gerbilbyte/DeMoN2/Kicad/DeMoN_2.0_PLCC/DeMoN_2.0_PLCC.kicad_sch

## KiCad design Kicad/DeMoN_2.0_PLCC/DeMoN_2.0_PLCC.kicad_sch (2025-10-27)

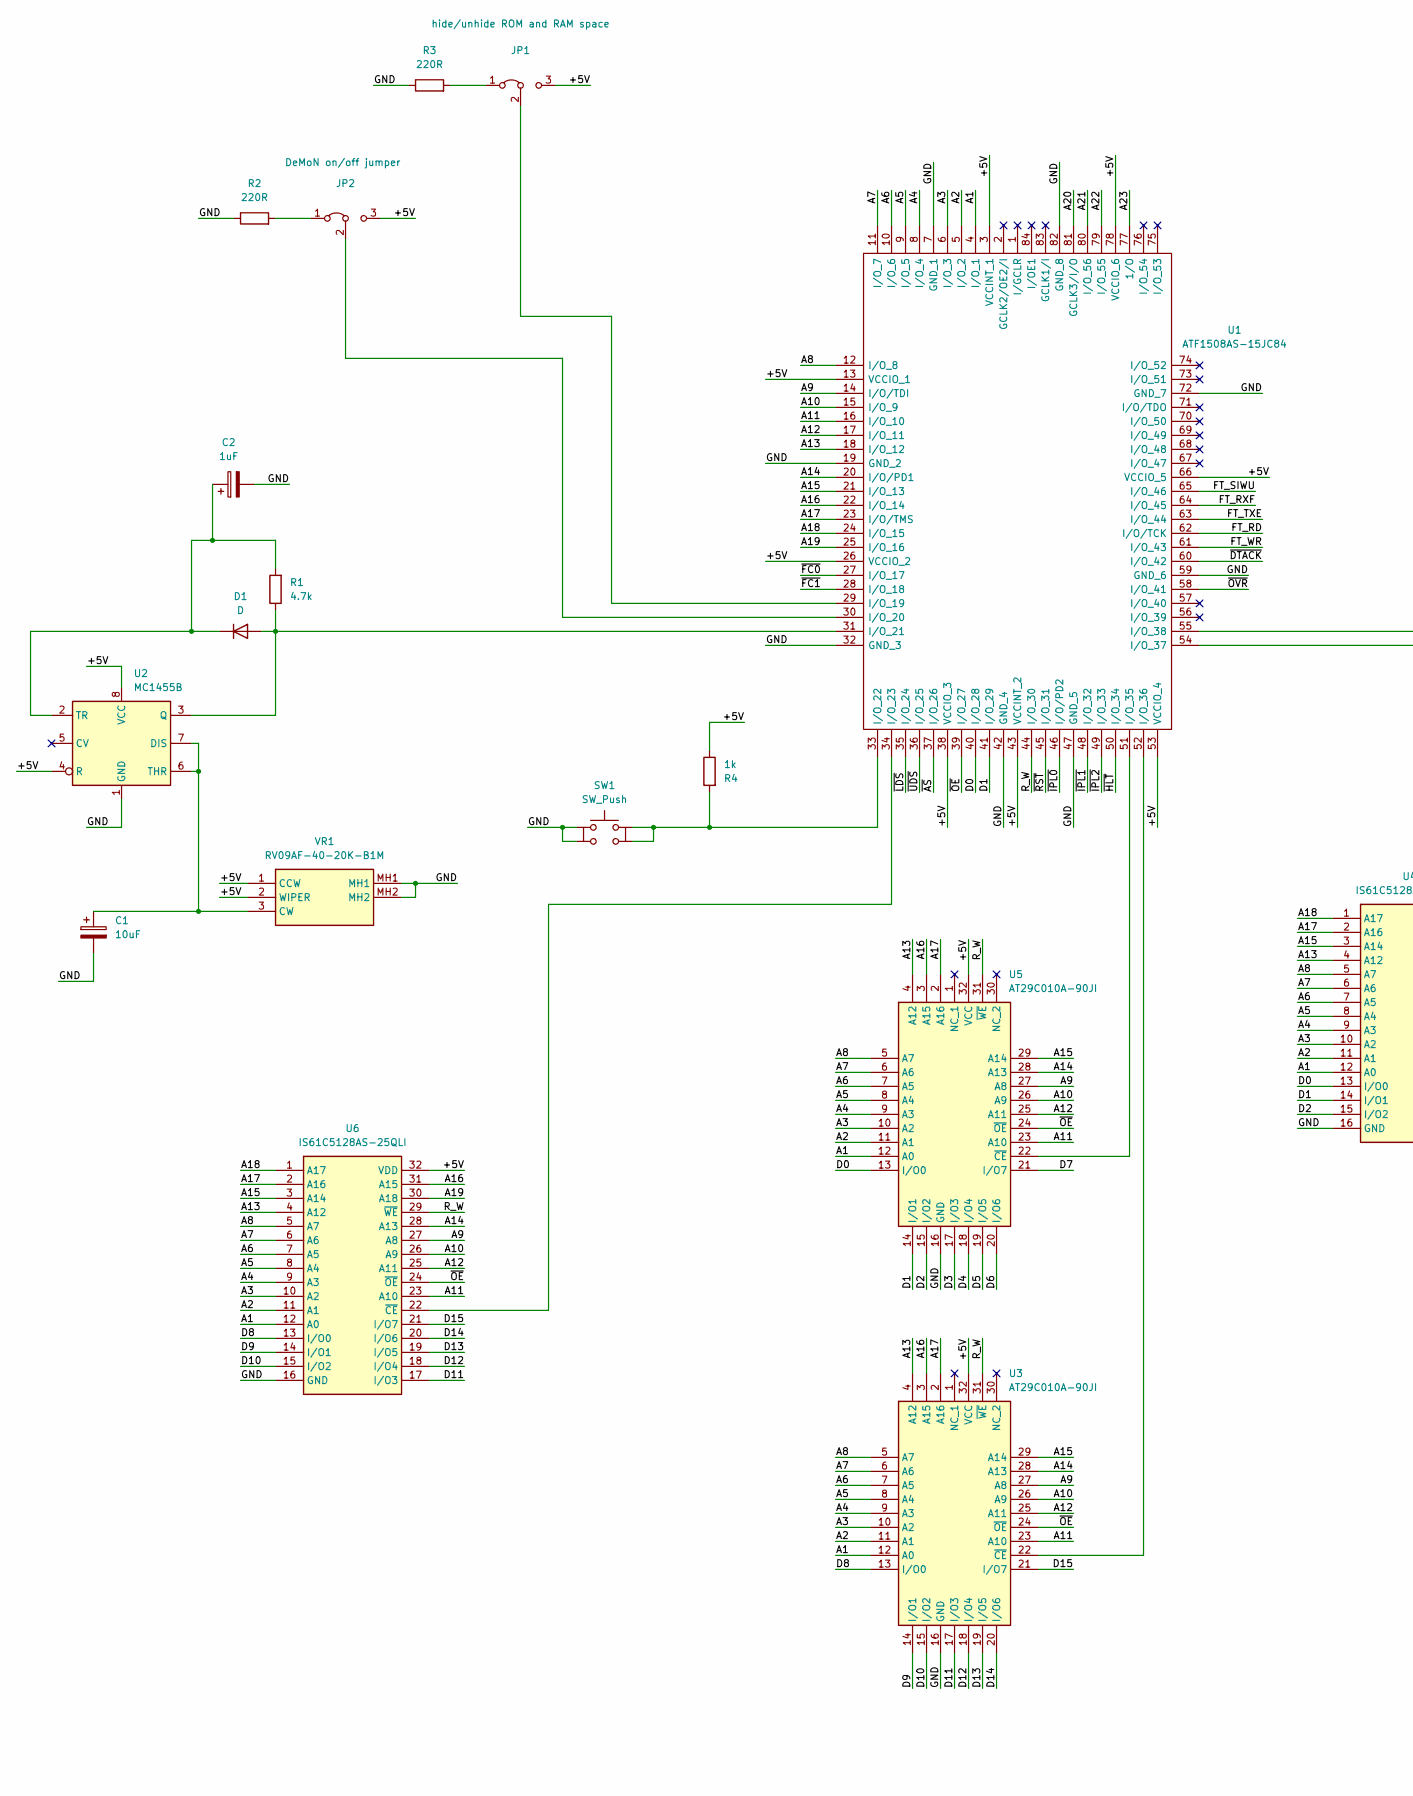
[picture p14: schematic DeMoN_2.0_PLCC.kicad_sch, part in row 1, column 1]

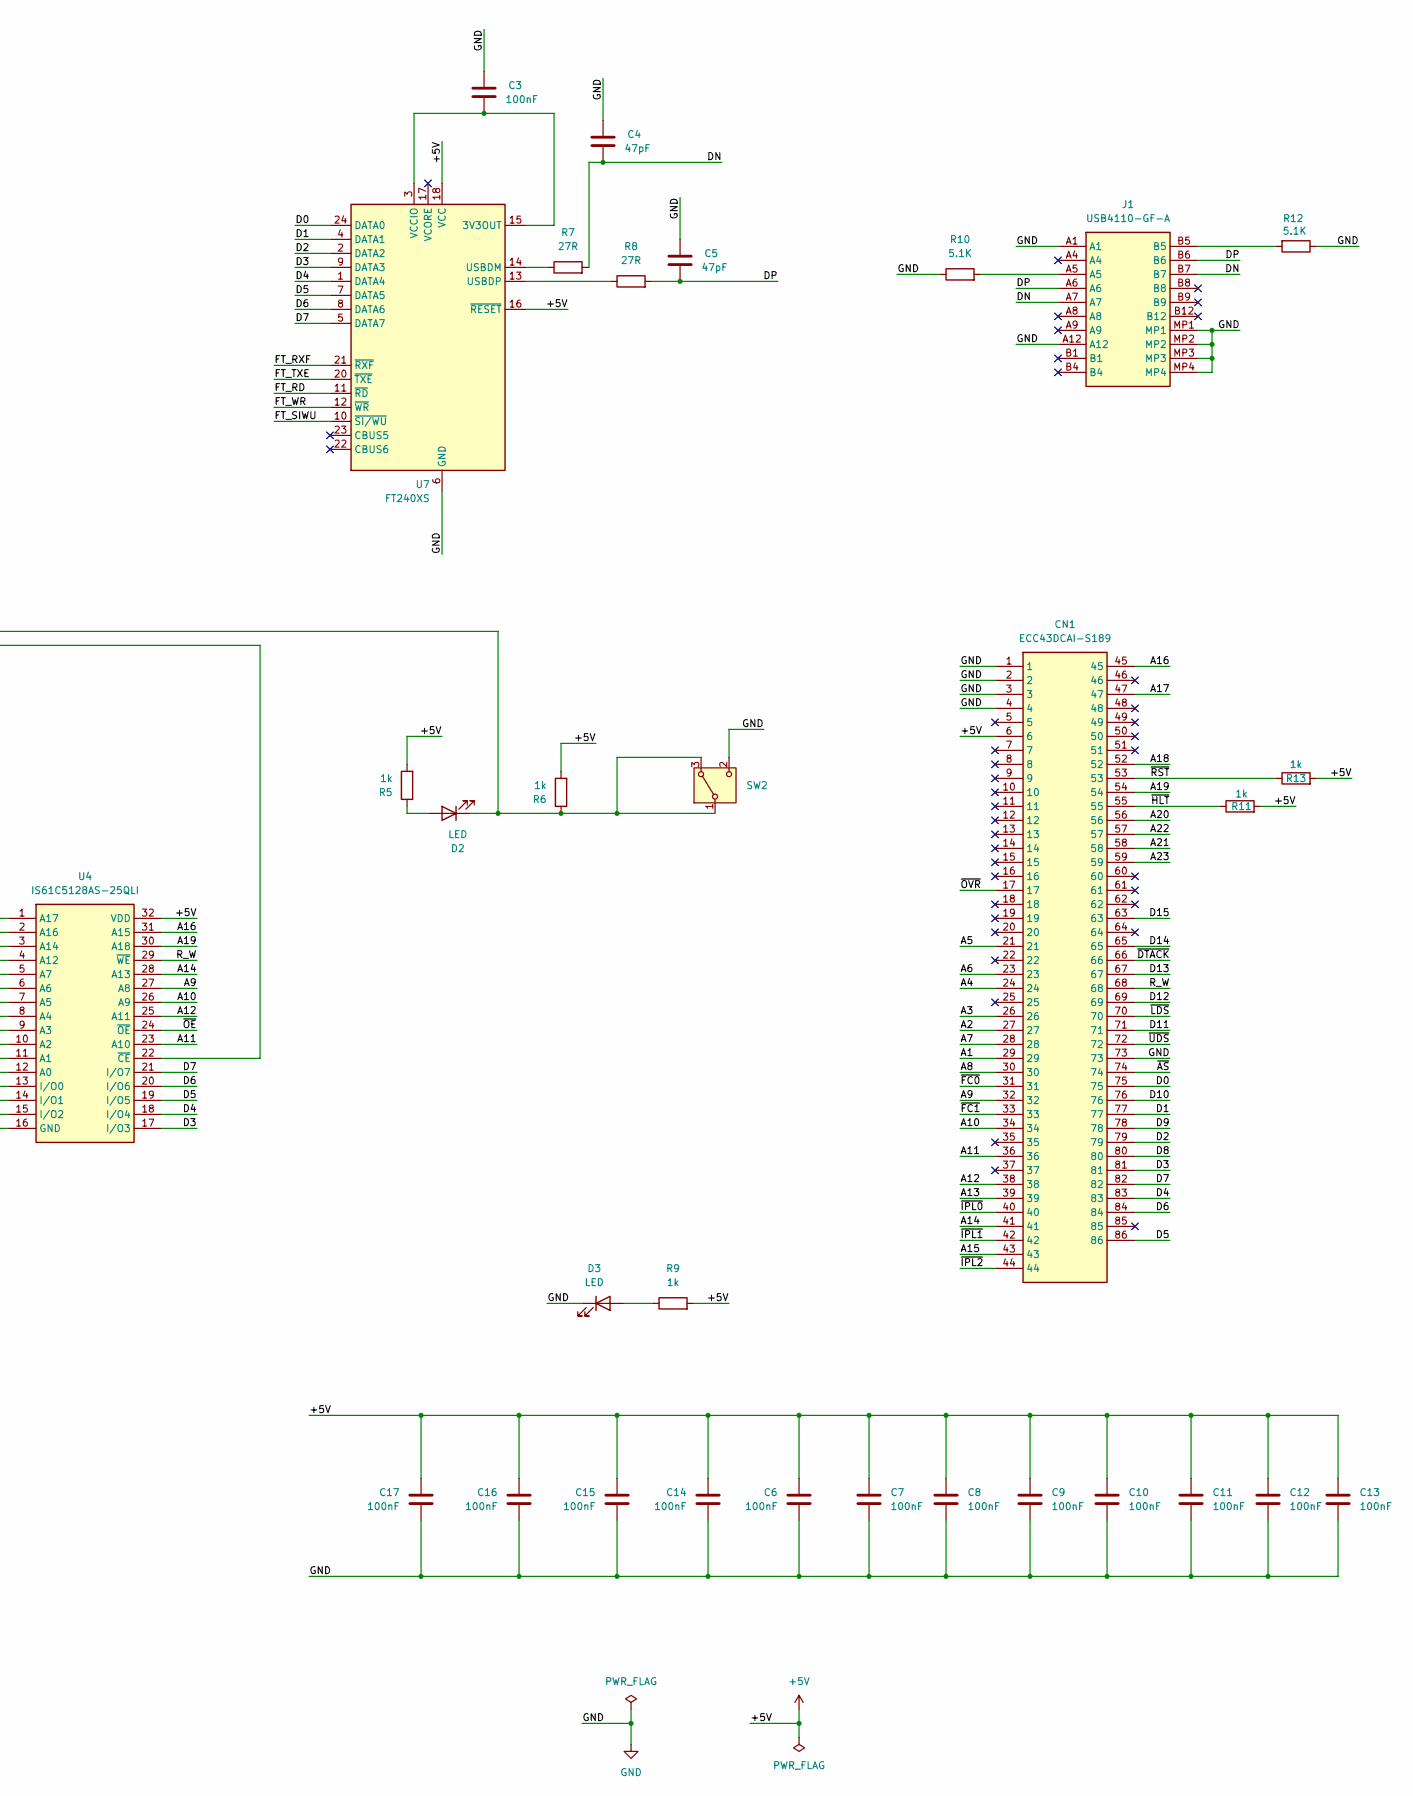
[picture p15: schematic DeMoN_2.0_PLCC.kicad_sch, part in row 1, column 2]

Parts:
C1: 10uF; CP_Radial_D5.0mm_P2.50mm
C2: 1uF; CP_Radial_D5.0mm_P2.50mm
C3, C6, C7, C8, C9, C10, C11, C12, C13, C14, C15, C16, C17: 100nF; C_1206_3216Metric_Pad1.33x1.80mm_HandSolder
C4, C5: 47pF; C_1206_3216Metric_Pad1.33x1.80mm_HandSolder
CN1: ECC43DCAI-S189; ECC43DCAIS189; Manufacturer_Part_Number ECC43DCAI-S189
D1: D; D_1206_3216Metric_Pad1.42x1.75mm_HandSolder
D2, D3: LED; LED_D3.0mm
J1: USB4110-GF-A; USB4110GFA; Mouser Part Number 640-USB4110-GF-A
JP1: hide/unhide ROM and RAM space; PinSocket_1x03_P2.54mm_Vertical
JP2: DeMoN on/off jumper; PinSocket_1x03_P2.54mm_Vertical
R1: 4.7k; R_1206_3216Metric_Pad1.30x1.75mm_HandSolder
R2, R3: 220R; R_1206_3216Metric_Pad1.30x1.75mm_HandSolder
R4, R5, R6, R9, R11, R13: 1k; R_1206_3216Metric_Pad1.30x1.75mm_HandSolder
R7, R8: 27R; R_1206_3216Metric_Pad1.30x1.75mm_HandSolder
R10, R12: 5.1K; R_1206_3216Metric_Pad1.30x1.75mm_HandSolder
SW1: SW_Push; SW_Push_2P1T_Toggle_CK_PVA1xxH1xxxxxxV2
SW2: SW_Wuerth_450301014042; SW_Slide-03_Wuerth-WS-SLTV_10x2.5x6.4_P2.54mm
U1: ATF1508AS-15JC84; PLCC-84_SMD-Socket; Manufacturer_Part_Number ATF1504AS-20JC84
U2: MC1455B; SOIC-8_3.9x4.9mm_P1.27mm
U3, U5: AT29C010A-90JI; PLCC-32_11.4x14.0mm_P1.27mm; Mouser Part Number 556-AT29C010A-90JI
U4, U6: IS61C5128AS-25QLI; SOIC127P1412X305-32N; Mouser Part Number 870-61C5128AS-25QLI
U7: FT240XS; SSOP-24_3.9x8.7mm_P0.635mm
VR1: RV09AF-40-20K-B1M; RV09AF4020KB1M; Mouser Part Number 317-2090F-1M

Connections:
+5V: C6.2, C7.1, C8.1, C9.1, C10.1, C11.1, C12.1, C13.2, C14.2, C15.2, C16.2, C17.2, CN1.6, JP1.3 (B), JP2.3 (B), R4.1, R5.2, R6.2, R9.2, R11.2, R13.2, U1.3 (VCCINT_1), U1.13 (VCCIO_1), U1.26 (VCCIO_2), U1.38 (VCCIO_3), U1.43 (VCCINT_2), U1.53 (VCCIO_4), U1.66 (VCCIO_5), U1.78 (VCCIO_6), U2.4 (R), U2.8 (VCC), U3.32 (VCC), U4.32 (VDD), U5.32 (VCC), U6.32 (VDD), U7.16 (~RESET), U7.18 (VCC), VR1.1 (CCW), VR1.2 (WIPER)
A1: CN1.29, U1.4 (I/O_1), U3.12 (A0), U4.12 (A0), U5.12 (A0), U6.12 (A0)
A2: CN1.27, U1.5 (I/O_2), U3.11 (A1), U4.11 (A1), U5.11 (A1), U6.11 (A1)
A3: CN1.26, U1.6 (I/O_3), U3.10 (A2), U4.10 (A2), U5.10 (A2), U6.10 (A2)
A4: CN1.24, U1.8 (I/O_4), U3.9 (A3), U4.9 (A3), U5.9 (A3), U6.9 (A3)
A5: CN1.21, U1.9 (I/O_5), U3.8 (A4), U4.8 (A4), U5.8 (A4), U6.8 (A4)
A6: CN1.23, U1.10 (I/O_6), U3.7 (A5), U4.7 (A5), U5.7 (A5), U6.7 (A5)
A7: CN1.28, U1.11 (I/O_7), U3.6 (A6), U4.6 (A6), U5.6 (A6), U6.6 (A6)
A8: CN1.30, U1.12 (I/O_8), U3.5 (A7), U4.5 (A7), U5.5 (A7), U6.5 (A7)
A9: CN1.32, U1.14 (I/O/TDI), U3.27 (A8), U4.27 (A8), U5.27 (A8), U6.27 (A8)
A10: CN1.34, U1.15 (I/O_9), U3.26 (A9), U4.26 (A9), U5.26 (A9), U6.26 (A9)
A11: CN1.36, U1.16 (I/O_10), U3.23 (A10), U4.23 (A10), U5.23 (A10), U6.23 (A10)
A12: CN1.38, U1.17 (I/O_11), U3.25 (A11), U4.25 (A11), U5.25 (A11), U6.25 (A11)
A13: CN1.39, U1.18 (I/O_12), U3.4 (A12), U4.4 (A12), U5.4 (A12), U6.4 (A12)
A14: CN1.41, U1.20 (I/O/PD1), U3.28 (A13), U4.28 (A13), U5.28 (A13), U6.28 (A13)
A15: CN1.43, U1.21 (I/O_13), U3.29 (A14), U4.3 (A14), U5.29 (A14), U6.3 (A14)
A16: CN1.45, U1.22 (I/O_14), U3.3 (A15), U4.31 (A15), U5.3 (A15), U6.31 (A15)
A17: CN1.47, U1.23 (I/O/TMS), U3.2 (A16), U4.2 (A16), U5.2 (A16), U6.2 (A16)
A18: CN1.52, U1.24 (I/O_15), U4.1 (A17), U6.1 (A17)
A19: CN1.54, U1.25 (I/O_16), U4.30 (A18), U6.30 (A18)
A20: CN1.56, U1.81 (GCLK3/I/O)
A21: CN1.58, U1.80 (I/O_56)
A22: CN1.57, U1.79 (I/O_55)
A23: CN1.59, U1.77 (1/O)
D0: CN1.75, U1.40 (I/O_28), U4.13 (I/O0), U5.13 (I/O0), U7.24 (DATA0)
D1: CN1.77, U1.41 (I/O_29), U4.14 (I/O1), U5.14 (I/O1), U7.4 (DATA1)
D2: CN1.79, U4.15 (I/O2), U5.15 (I/O2), U7.2 (DATA2)
D3: CN1.81, U4.17 (I/O3), U5.17 (I/O3), U7.9 (DATA3)
D4: CN1.83, U4.18 (I/O4), U5.18 (I/O4), U7.1 (DATA4)
D5: CN1.86, U4.19 (I/O5), U5.19 (I/O5), U7.7 (DATA5)
D6: CN1.84, U4.20 (I/O6), U5.20 (I/O6), U7.8 (DATA6)
D7: CN1.82, U4.21 (I/O7), U5.21 (I/O7), U7.5 (DATA7)
D8: CN1.80, U3.13 (I/O0), U6.13 (I/O0)
D9: CN1.78, U3.14 (I/O1), U6.14 (I/O1)
D10: CN1.76, U3.15 (I/O2), U6.15 (I/O2)
D11: CN1.71, U3.17 (I/O3), U6.17 (I/O3)
D12: CN1.69, U3.18 (I/O4), U6.18 (I/O4)
D13: CN1.67, U3.19 (I/O5), U6.19 (I/O5)
D14: CN1.65, U3.20 (I/O6), U6.20 (I/O6)
D15: CN1.63, U3.21 (I/O7), U6.21 (I/O7)
DN: C4.2, J1.A7, J1.B7, R7.2
DP: C5.2, J1.A6, J1.B6, R8.2
FT_RD: U1.62 (I/O/TCK), U7.11 (~RD)
FT_RXF: U1.64 (I/O_45), U7.21 (~RXF)
FT_SIWU: U1.65 (I/O_46), U7.10 (~SI/WU)
FT_TXE: U1.63 (I/O_44), U7.20 (~TXE)
FT_WR: U1.61 (I/O_43), U7.12 (~WR)
GND: C1.2, C2.2, C3.1, C4.1, C5.1, C6.1, C7.2, C8.2, C9.2, C10.2, C11.2, C12.2, C13.1, C14.1, C15.1, C16.1, C17.1, CN1.1, CN1.2, CN1.3, CN1.4, CN1.73, D3.1 (K), J1.A1, J1.A12, J1.MP1, J1.MP2, J1.MP3, J1.MP4, R2.1, R3.1, R10.1, R12.1, SW1.2, SW1.4, SW2.2 (C), U1.7 (GND_1), U1.19 (GND_2), U1.32 (GND_3), U1.42 (GND_4), U1.47 (GND_5), U1.59 (GND_6), U1.72 (GND_7), U1.82 (GND_8), U2.1 (GND), U3.16 (GND), U4.16 (GND), U5.16 (GND), U6.16 (GND), U7.6 (GND), U7.19 (GND), VR1.MH1, VR1.MH2
unnamed: C1.1, U2.6 (THR), U2.7 (DIS), VR1.3 (CW)
unnamed: C2.1, D1.1 (K), R1.2, U2.2 (TR)
unnamed: C3.2, U7.3 (VCCIO), U7.15 (3V3OUT)
unnamed: D1.2 (A), R1.1, U1.31 (I/O_21), U2.3 (Q)
unnamed: D2.1 (K), R6.1, SW2.1 (B), SW2.3 (A), U1.55 (I/O_38)
unnamed: D2.2 (A), R5.1
unnamed: D3.2 (A), R9.1
unnamed: J1.A5, R10.2
unnamed: J1.B5, R12.2
unnamed: JP1.1 (A), R3.2
unnamed: JP1.2 (C), U1.29 (I/O_19)
unnamed: JP2.1 (A), R2.2
unnamed: JP2.2 (C), U1.30 (I/O_20)
unnamed: R4.2, SW1.1, SW1.3, U1.33 (I/O_22)
unnamed: R7.1, U7.14 (USBDM)
unnamed: R8.1, U7.13 (USBDP)
unnamed: U1.34 (I/O_23), U6.22 (~CE)
unnamed: U1.51 (I/O_35), U5.22 (~CE)
unnamed: U1.52 (I/O_36), U3.22 (~CE)
unnamed: U1.54 (I/O_37), U4.22 (~CE)
R_W: CN1.68, U1.44 (I/O_30), U3.31 (~WE), U4.29 (~WE), U5.31 (~WE), U6.29 (~WE)
~AS: CN1.74, U1.37 (I/O_26)
~DTACK: CN1.66, U1.60 (I/O_42)
~FC0: CN1.31, U1.27 (I/O_17)
~FC1: CN1.33, U1.28 (I/O_18)
~HLT: CN1.55, R11.1, U1.50 (I/O_34)
~IPL0: CN1.40, U1.46 (I/O/PD2)
~IPL1: CN1.42, U1.48 (I/O_32)
~IPL2: CN1.44, U1.49 (I/O_33)
~LDS: CN1.70, U1.35 (I/O_24)
~OE: U1.39 (I/O_27), U3.24 (~OE), U4.24 (~OE), U5.24 (~OE), U6.24 (~OE)
~OVR: CN1.17, U1.58 (I/O_41)
~RST: CN1.53, R13.1, U1.45 (I/O_31)
~UDS: CN1.72, U1.36 (I/O_25)
